Ducktronix/PrISM64/Hardware/SolidWorks/AcrylicPanelSides.SLDPRT

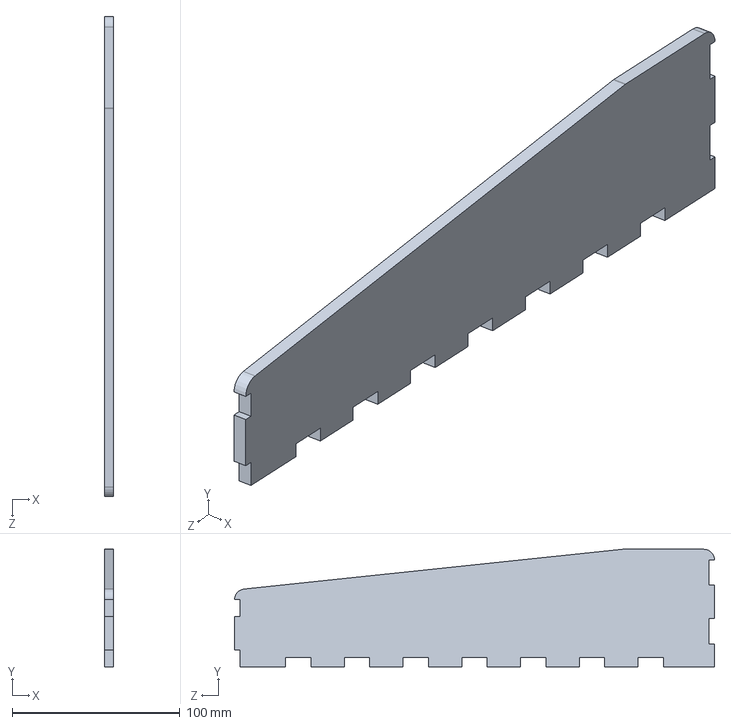
[picture p15: CAD file, 2014-03-06]
Hardware/SolidWorks/AcrylicPanelSides.SLDPRT
5.59 x 70.0 x 286.0 mm
