Ducktronix/PrISM64/Hardware/SolidWorks/35mmArcadeButton_Sparkfun.SLDPRT

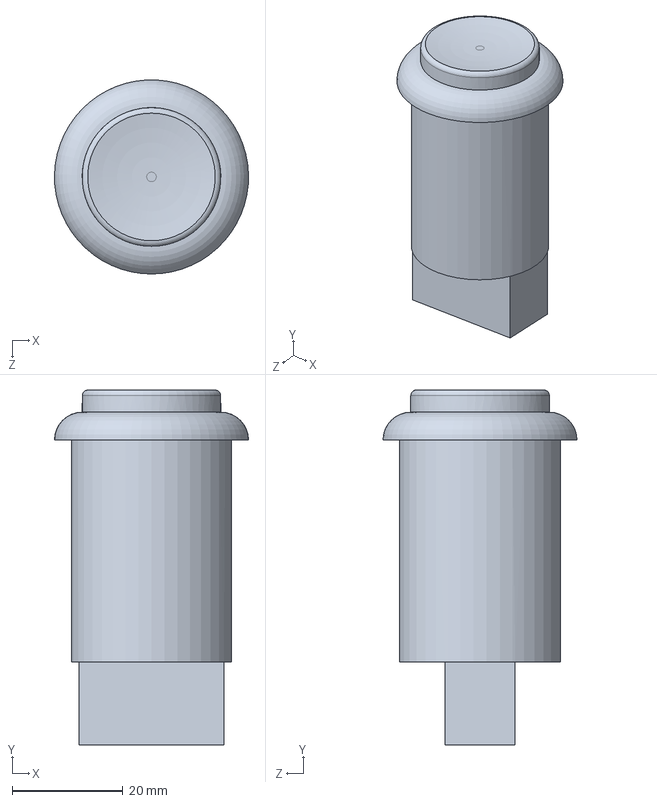
[picture p16: CAD file, 2014-03-06]
Hardware/SolidWorks/35mmArcadeButton_Sparkfun.SLDPRT
35.0 x 64.0 x 35.0 mm
