Ducktronix/PrISM64/Hardware/SolidWorks/Slider Knob MULTICOMP  MC21076.SLDPRT

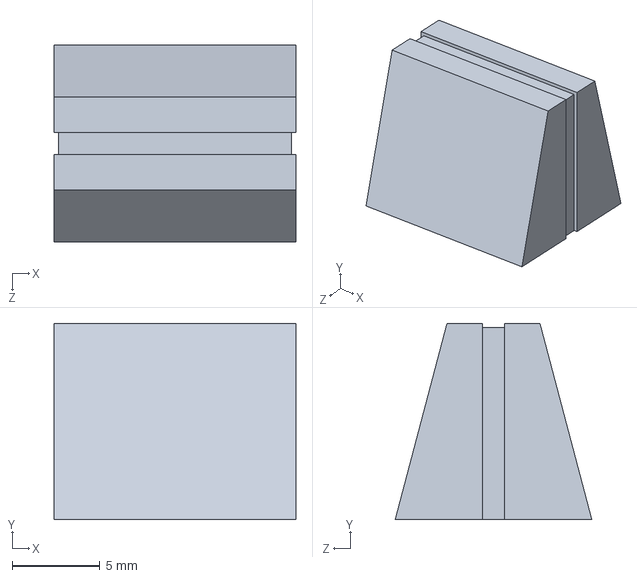
[picture p17: CAD file, 2014-03-06]
Hardware/SolidWorks/Slider Knob MULTICOMP MC21076.SLDPRT
13.8 x 11.2 x 11.2 mm
