Ducktronix/PrISM64/Hardware/SolidWorks/MatrixBezelPrototype.SLDPRT

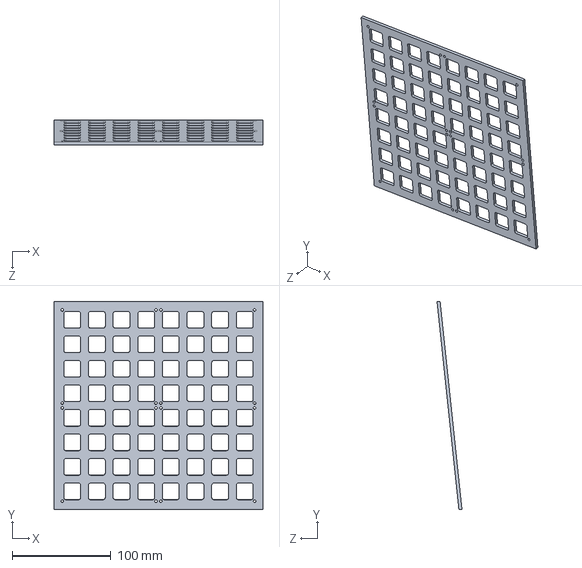
[picture p18: CAD file, 2014-02-26]
Hardware/SolidWorks/MatrixBezelPrototype.SLDPRT
212.0 x 211.2 x 25.3 mm
