Ducktronix/PrISM64/Hardware/SolidWorks/MatrixCrossmember.SLDPRT

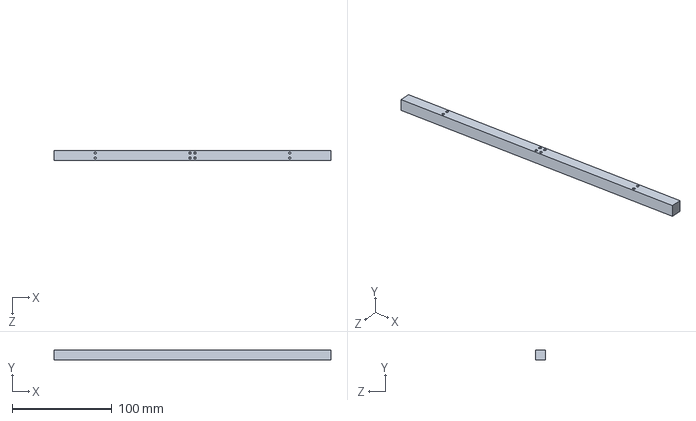
[picture p19: CAD file, 2014-02-26]
Hardware/SolidWorks/MatrixCrossmember.SLDPRT
277.4 x 10.0 x 10.0 mm
