Ducktronix/PrISM64/Hardware/SolidWorks/FloorPan.SLDPRT

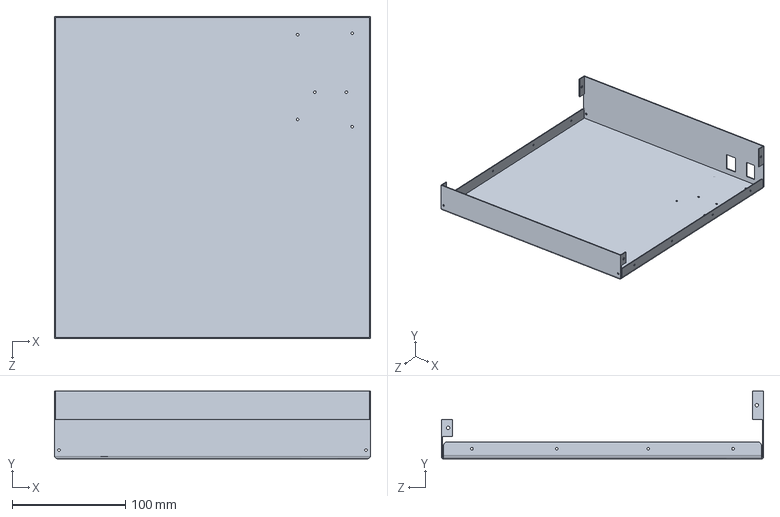
[picture p20: CAD file, 2014-02-26]
Hardware/SolidWorks/FloorPan.SLDPRT
279.4 x 60.0 x 285.0 mm
