Ducktronix/PrISM64/Hardware/SolidWorks/8 PORT HEADER.SLDPRT

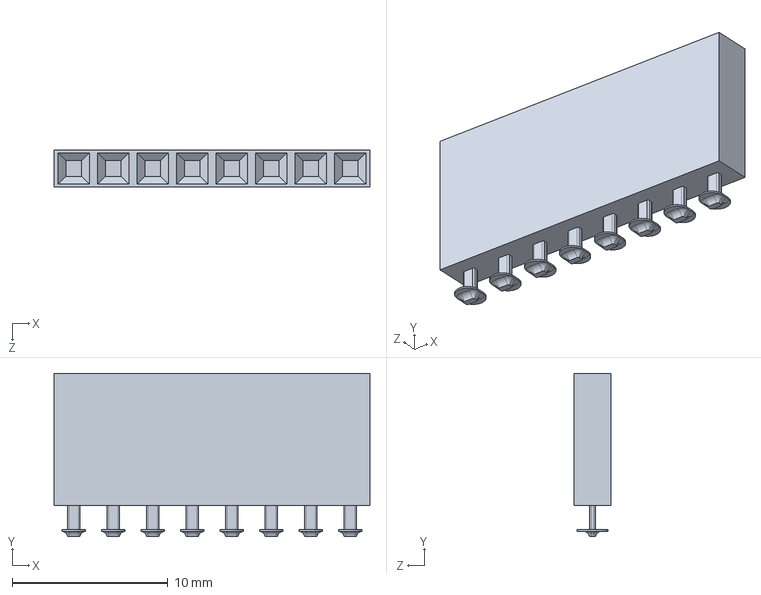
[picture p21: CAD file, 2014-02-14]
Hardware/SolidWorks/8 PORT HEADER.SLDPRT
20.3 x 10.5 x 2.41 mm
