Ducktronix/PrISM64/Hardware/SolidWorks/7mm Standoff.SLDPRT

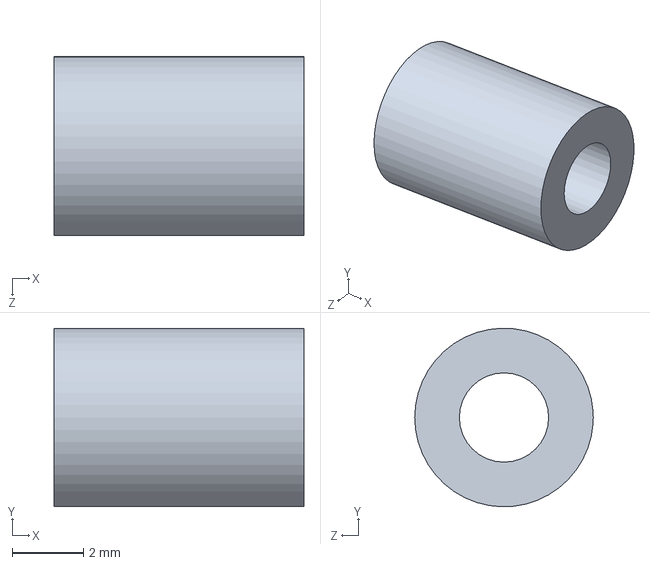
[picture p22: CAD file, 2014-02-14]
Hardware/SolidWorks/7mm Standoff.SLDPRT
7.00 x 5.00 x 5.00 mm
