Ducktronix/PrISM64/Hardware/SolidWorks/8pin_header__M.SLDPRT

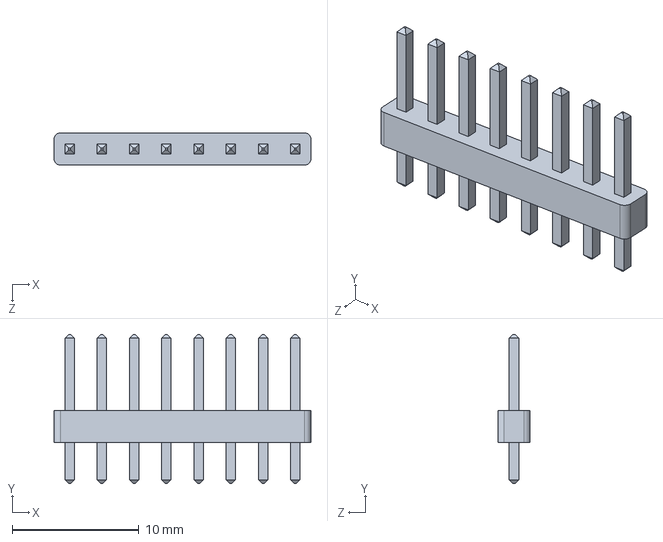
[picture p23: CAD file, 2014-02-14]
Hardware/SolidWorks/8pin_header__M.SLDPRT
20.2 x 11.8 x 2.54 mm
