Ducktronix/PrISM64/Hardware/SolidWorks/10pin_header__M.SLDPRT

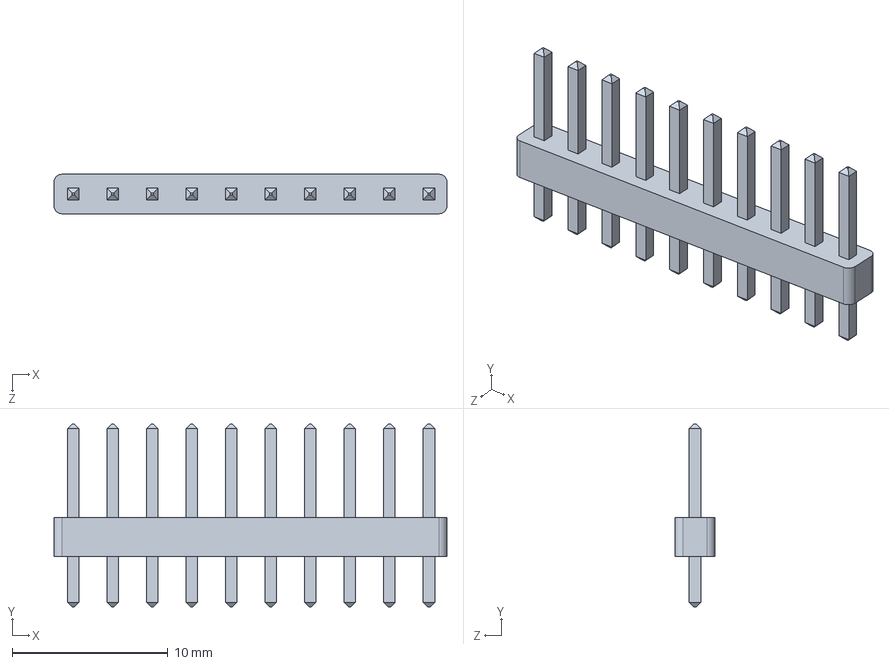
[picture p24: CAD file, 2014-02-14]
Hardware/SolidWorks/10pin_header__M.SLDPRT
25.2 x 11.8 x 2.54 mm
