Ducktronix/PrISM64/Hardware/SolidWorks/FloorPanCrossMember.SLDPRT

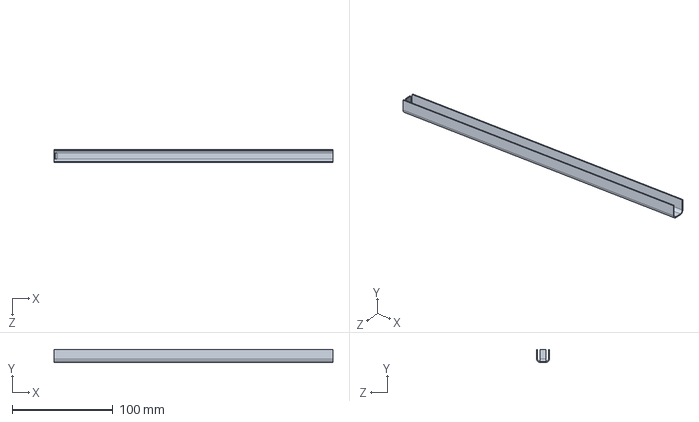
[picture p25: CAD file, 2014-02-14]
Hardware/SolidWorks/FloorPanCrossMember.SLDPRT
276.9 x 12.7 x 12.7 mm
