Ducktronix/PrISM64/Hardware/SolidWorks/MatrixPCB.SLDPRT

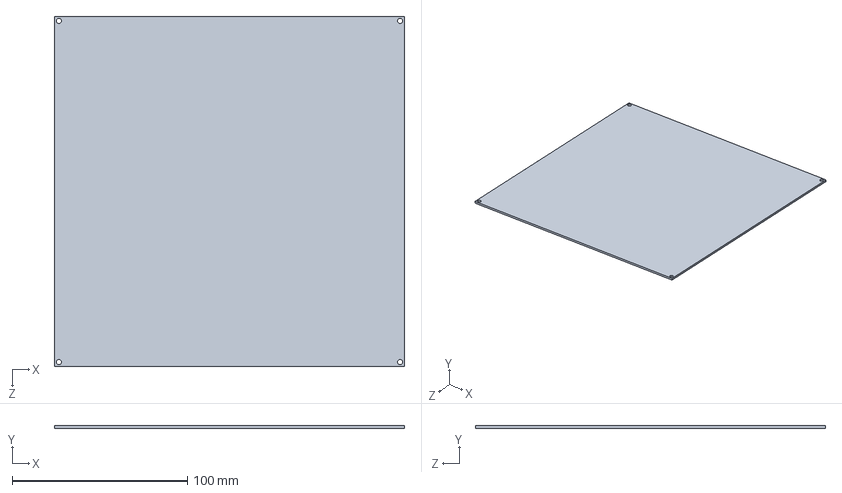
[picture p26: CAD file, 2014-02-14]
Hardware/SolidWorks/MatrixPCB.SLDPRT
200.0 x 1.60 x 200.0 mm
