Ducktronix/PrISM64/Hardware/SolidWorks/AngleAluminum half in.SLDPRT

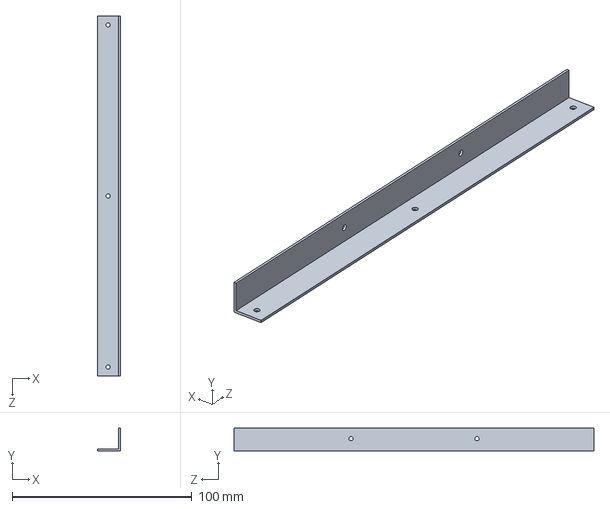
[picture p27: CAD file, 2014-02-14]
Hardware/SolidWorks/AngleAluminum half in.SLDPRT
12.7 x 12.7 x 200.0 mm
