Ducktronix/PrISM64/Hardware/SolidWorks/18pin_header__M.SLDPRT

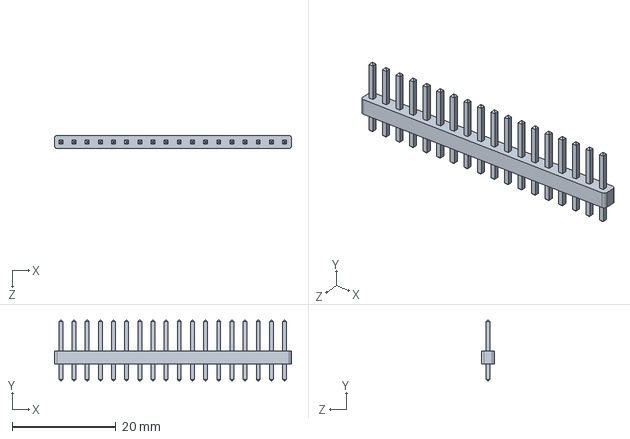
[picture p28: CAD file, 2014-02-14]
Hardware/SolidWorks/18pin_header__M.SLDPRT
45.8 x 11.8 x 2.54 mm
