Ducktronix/PrISM64/Hardware/SolidWorks/6 PORT HEADER.SLDPRT

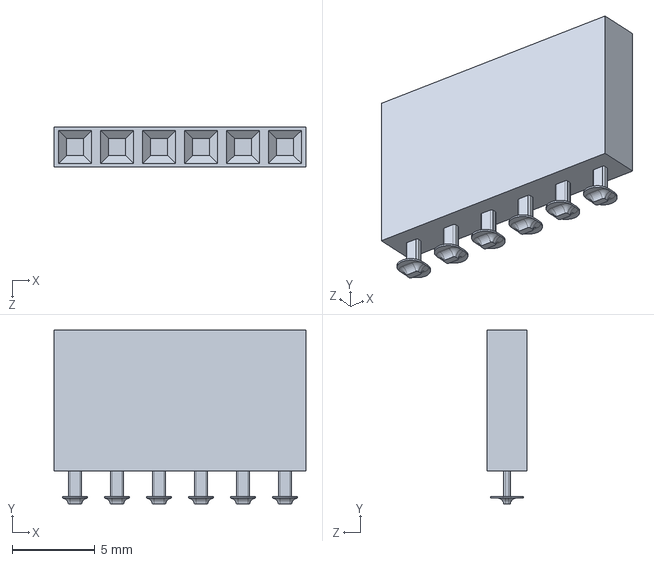
[picture p29: CAD file, 2014-02-14]
Hardware/SolidWorks/6 PORT HEADER.SLDPRT
15.2 x 10.5 x 2.41 mm
