Ducktronix/PrISM64/Hardware/SolidWorks/ArduinoShieldPCB.SLDPRT

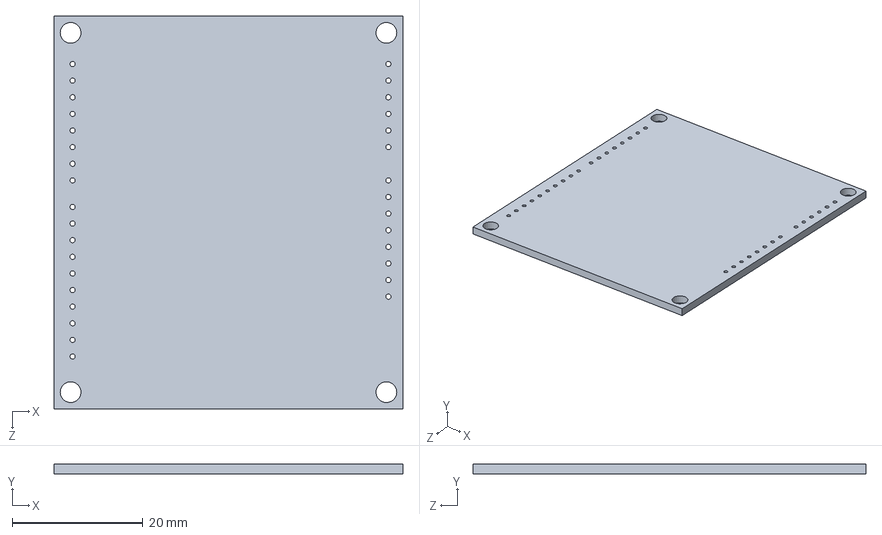
[picture p30: CAD file, 2014-02-14]
Hardware/SolidWorks/ArduinoShieldPCB.SLDPRT
53.3 x 1.60 x 60.0 mm
