Ducktronix/PrISM64/Hardware/SolidWorks/AcrylicPanelSideSupport.SLDPRT

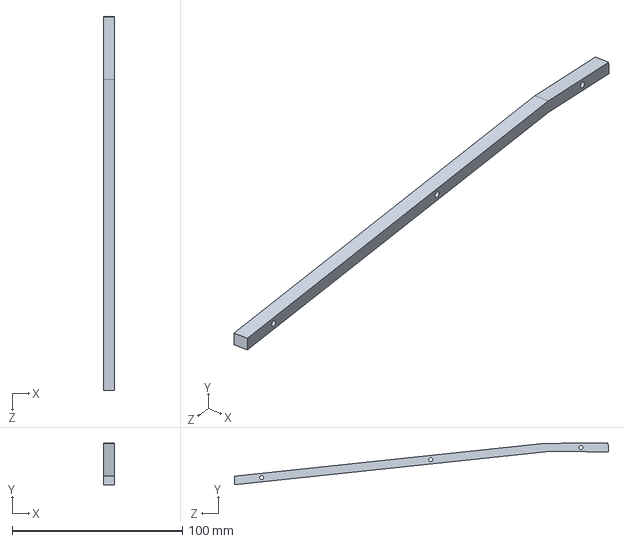
[picture p31: CAD file, 2014-02-14]
Hardware/SolidWorks/AcrylicPanelSideSupport.SLDPRT
6.35 x 24.4 x 219.9 mm
