Ducktronix/PrISM64/Hardware/SolidWorks/AcrylicPanel.SLDPRT

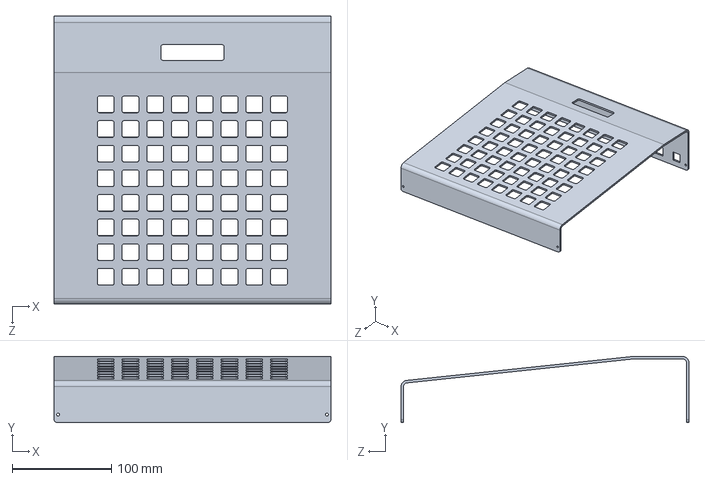
[picture p32: CAD file, 2014-02-14]
Hardware/SolidWorks/AcrylicPanel.SLDPRT
279.4 x 66.7 x 290.8 mm
