Ducktronix/PrISM64/Hardware/SolidWorks/Silicone 4x4 Button Matrix.SLDPRT

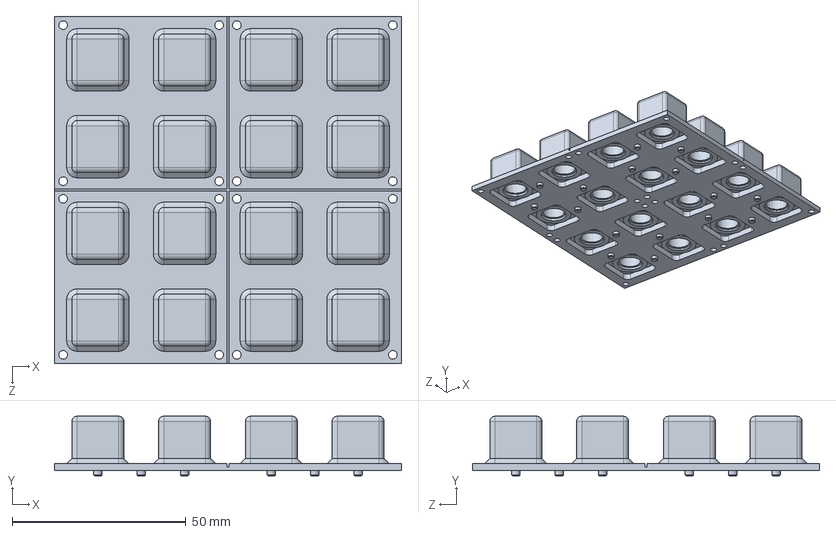
[picture p33: CAD file, 2014-02-12]
Hardware/SolidWorks/Silicone 4x4 Button Matrix.SLDPRT
100.0 x 17.2 x 100.0 mm
